sdp8483/train_horn/images/Train_Horn_AmpJP.png

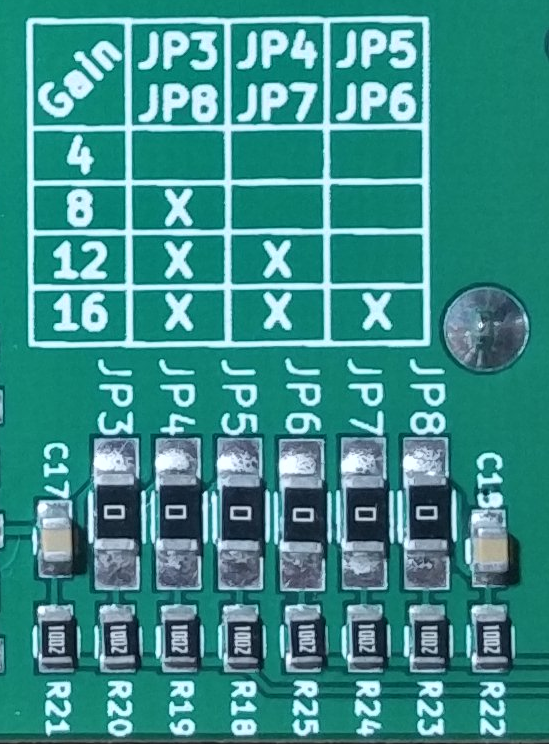
images/Train_Horn_AmpJP.png
