sdp8483/train_horn/images/Train_Horn_filter.png

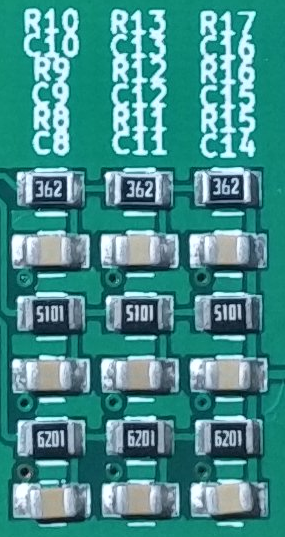
images/Train_Horn_filter.png
