sdp8483/train_horn/3d_models/Generic_5mm_2Pos_TerminalBlock.step

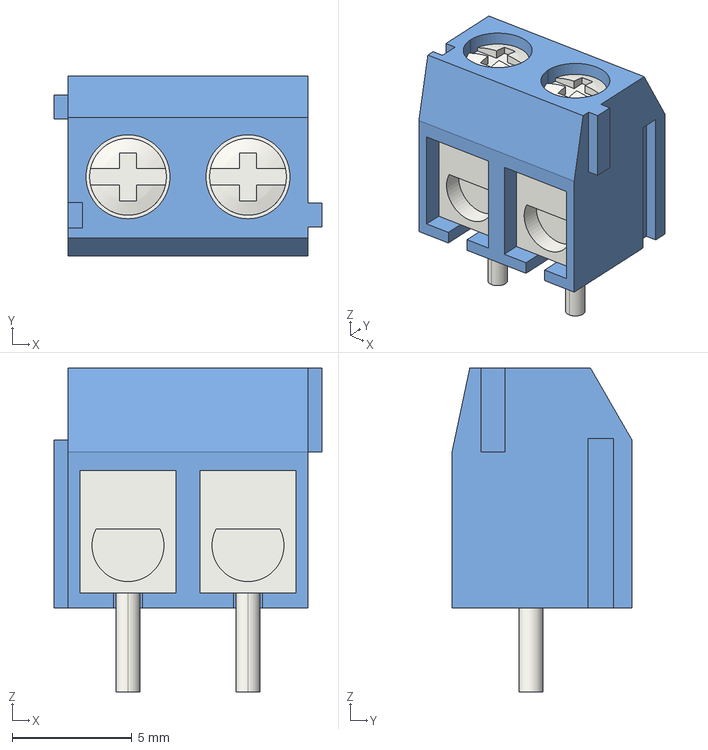
[picture p33: CAD file, 2018-02-19]
3d_models/Generic_5mm_2Pos_TerminalBlock.step
11.2 x 7.50 x 13.5 mm
