sdp8483/train_horn/3d_models/VLP_450_F.step

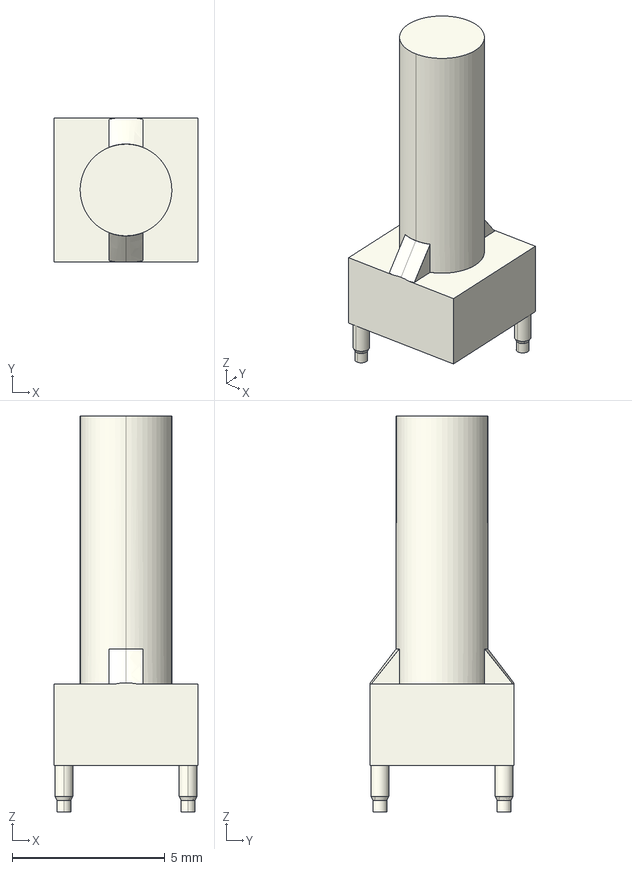
[picture p34: CAD file, 2018-02-19]
3d_models/VLP_450_F.step
4.70 x 4.70 x 13.0 mm
